freevariode/FreeVarioGauge/src/FreeVarioGauge/data/FreeVario_194x156.bmp

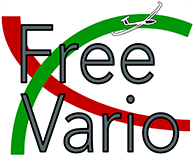
src/FreeVarioGauge/data/FreeVario_194x156.bmp
