freevariode/FreeVarioGauge/src/FreeVarioGauge/FreeVarioGauge.ino

//    OpenVarioGauge is a programm to generate the vario display using NMEA Output
//    of OpenVario.
//    Copyright (C) 2019  Dirk Jung Blaubart@gmx.de
//
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
//*************************************************
//****  Screen and SPIFFS Headers and Defines  ****
//*************************************************
#include <Streaming.h>
#include <WiFi.h>
#include <WebServer.h>
#include <ESPmDNS.h>
#include <Update.h>
#include <SPI.h>
#include <TFT_eSPI.h>
#include <Preferences.h>
Preferences prefs;

#include "LogoOV.h"
#include "FS.h"
#include "SPIFFS.h"
#include <ESP32Encoder.h>

ESP32Encoder Vario_Enc;

#define RXD2 16                // PIN 27
#define TXD2 17                // PIN 28
#define VE_PB 27               // PIN 12
#define DEG2RAD 0.0174532925
#define STF_MODE 13            // PIN 16
#define STF_AUTO 33            // PIN 9
#define OuterRadius 160
#define InnerRadius 130
#define xCenter 160
#define yCenter 160
#define BLUE 0x04df

static TFT_eSPI tft = TFT_eSPI();
TFT_eSprite nameOfField = TFT_eSprite(&tft);
TFT_eSprite Name = TFT_eSprite(&tft);
TFT_eSprite smallFont = TFT_eSprite(&tft);
TFT_eSprite needleGreen = TFT_eSprite(&tft);
TFT_eSprite needleBlue = TFT_eSprite(&tft);
TFT_eSprite drawOuterLine = TFT_eSprite(&tft);
TFT_eSprite drawColoredArc = TFT_eSprite(&tft);
TFT_eSprite drawRectangle = TFT_eSprite(&tft);
TFT_eSprite number = TFT_eSprite(&tft);
TFT_eSprite background = TFT_eSprite(&tft);
WebServer server(80);

Print &cout = Serial;
TaskHandle_t SerialScanTask, TaskValueRefresh;

SemaphoreHandle_t xTFTSemaphore;

long NOT_SET = -1;
long pushButtonPressTime = NOT_SET;

const String SOFTWARE_VERSION = "  V2.4.4 - 2025";

const char *host = "FreeVario_Displayboard";
const char *ssid = "FV_Displayboard";
const char *password = "12345678";


String displayMode = "Waiting ...";
String soundMode = "Waiting ...";
String displayIP = "";
String soundIP = "";
String nameSetting = "QNH";
String nameSpeed = "NA";
String nameHight = "NA";
String stf_mode = "Vario";
String valueQnhAsString = "1013";
String valueBugAsString = "0";
String valueMuteAsString = "NA";
String valueWindAsString = "NA";
String valueSTFAsString = "NA";
String valueAttenAsString = "2";
String valueGrsAsString = "0";
String valueTasAsString = "0";
String valueVaaAsString = "+0.0";
String valueVanAsString = "+0.0";
String valueHigAsString = "0";
String valueFLAsString = "0";
String valueHagAsString = "0";
String valueAwsAsString = "0";
String valueCwsAsString = "0";
String valueMacAsString = "0.0";
String voltage = "0.0";
String UTC = "00:00";
String UTCHour = "00";
String UTCMinute = "00";
String valueVoltageAsString = "0.0";

extern uint16_t logoOV[];

float var = 0;
float stf = 0.0;
float valueTasAsFloat = 0;
float valueMacAsFloat = 0.5;
float valueAwsAsFloat = -1000;
float valueCwsAsFloat = -1000;
float valueAwdAsFloat = -1000;
float valueCwdAsFloat = -1000;
float valueHeaAsFloat = 0;
float encoderPosition = (float) - 999;
float menuActiveSince = 0;                  // Will be updated in menu run

double valueQnhAsFloat = 1013;
double valueBugAsFloat = 0;

bool loadMenuFont = true;
bool loadMenuArc = true;
bool updatemode = false;
bool showBootscreen = true;
bool mci = false;
bool pushButtonIsLongpress = false;
bool pushButtonIsShortpress = false;
bool pushButtonPressed = false;
bool encoderLeft = false;
bool encoderRight = false;
bool encoderWasMoved = false;
bool menuWasTriggered = false;
bool subMenuTriggered = false;
bool subMenuLevelTwoTriggered = false;
bool requestMenuPaint = false;
bool WasSend = false;
bool AutoWasSend = false;
bool SourceIsXCSoar = false;
bool SourceIsLarus = false;

int MENU_SPEED_TYP = 1;
int MENU_HIGHT_TYP = 2;
int MENU_VALUE_TYP = 3;
int MENU_VALUE_QNH = 1;
int MENU_VALUE_BUG = 2;
int MENU_VALUE_MUTE = 3;
int k = 0;
int stf_mode_state;
int startAngle, segmentDraw, segmentCount;
int Wificount = 0;
int valueMuteAsInt;
int valueAttenAsInt;
int valueWindAsInt;
int valueSTFAsInt;
int changeMode;
int oldChangeMode;
int offset = 0;
int selectedMenu = MENU_SPEED_TYP;
int requestDrawMenu = 1;
int requestDrawMenuLevel = 0;
int TimeDifference = 0;

unsigned long lastTimeBoot = 0;
unsigned long lastTimeReady = 0;
unsigned long mcSend  = 0;
unsigned long stayAlive = 0;

// ************************************
// ****  Initialize SPIFFS memory  ****
// ************************************
void SPIFFSstart() {
  if (!SPIFFS.begin()) {
    Serial.println("SPIFFS initialisation failed!");
    while (1) yield(); // Stay here twiddling thumbs waiting
  }
  Serial.println("\r\nInitialisation done.");
}
