freevariode/FreeVarioGauge/src/FreeVarioGauge/LogoOV.h

#include <pgmspace.h>

uint16_t logoOV[] PROGMEM = {
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

};
