freevariode/FreeVarioGauge/src/VarioSound_V2.x/SerialScan.ino

//****************************
//****  read serial port  ****
//****************************
void SerialScan () {
  unsigned long lastTimeSerial2 = 0;
  if (updatemode == false) {
    WiFi.mode(WIFI_OFF);
    char Data;
    String DataString;
    if (Serial2.available()) {
      Data = Serial2.read();
      if (Data == '$') {
        while (Data != 10) {
          if (Data >= 32 && Data <= 126) {
            DataString += Data;
          }
          Data = Serial2.read();
        }
        startSound = true;
        //Serial.println(DataString);
      }
      else {
        if ((!SourceIsXCSoar && !SourceIsLarus) && (baudDetect == 0) && (millis() - ChangeBaud <= 5000)) {
          Serial2.end();
          Serial.println("Looking for XCSoar");
          Serial.println("baud rate is set to 115200");
          Serial2.begin(115200, SERIAL_8N1, RXD2, TXD2);
          delay(500);
          baudDetect = 1;
        }
        else if ((!SourceIsXCSoar && !SourceIsLarus) && (baudDetect == 1) &&  (millis() - ChangeBaud > 5000) && (millis() - ChangeBaud <= 10000)) {
          Serial2.end();
          Serial.println("Looking for Larus");
          Serial.println("baud rate is set to 38400");
          Serial2.begin(38400, SERIAL_8N1, RXD2, TXD2);
          delay(500);
          baudDetect = 0;
        }
        else if ((!SourceIsXCSoar && !SourceIsLarus) && (millis() - ChangeBaud > 10000)) {
          ChangeBaud = millis();
        }
      }

      //****************************
      //****  XCSoar is source  ****
      //****************************
      if ((DataString.startsWith("$PFV,VAR")) || (DataString.startsWith("$PFV,VAN"))) {
        if (!SourceIsXCSoar) {
          SourceIsXCSoar = true;
          SourceIsLarus = false;
        }
      }

      if (DataString.startsWith("$PFV") && SourceIsXCSoar == true) {
        //Serial2.println(DataString);
        int pos = DataString.indexOf(',');
        DataString.remove(0, pos + 1);
        int pos1 = DataString.indexOf(',');                   //finds the place of the first,
        String variable = DataString.substring(0, pos1);      //captures the first record
        int pos2 = DataString.indexOf('*', pos1 + 1 );        //finds the place of *
        String wert = DataString.substring(pos1 + 1, pos2);   //captures the second record

        //**************************************
        //****  Analysis of the climb rate  ****
        //**************************************
        if (variable == "VAR") {
          var = wert.toFloat();
          varAvailable = true;
        }

        //***********************************************
        //****  Analysis of the current XCSoar mode  ****
        //***********************************************
        if (variable == "MOD") {
          mod = wert;
        }

        //*******************************************************
        //****  Analysis of the current Remote control mode  ****
        //*******************************************************
        if (variable == "REM") {
          rem = wert;
        }

        //*****************************************
        //****  Analysis of the true airspeed  ****
        //*****************************************
        if (variable == "TAS") {
          tas = wert.toFloat();
        }

        //************************************
        //****  Analysis of speed to fly  ****
        //************************************
        if (variable == "STF") {
          stfValue = wert.toFloat();
          if (tas > 10) {
            int FF = (valueAttenAsInt * 10) + 1;
            stf = filter(stfValue, FF);
          }
          else {
            stf = tas;
          }
        }

        //*************************
        //****  Analysis Mute  ****
        //*************************
        else if (variable == "MUT") {
          valueMuteAsInt = wert.toInt();
        }

        //********************************
        //****  Analysis Attenuation  ****
        //********************************
        else if (variable == "ATT") {
          valueAttenAsInt = wert.toInt();
        }

        //*******************************
        //****  analyse STF-Mode  ****
        //*******************************
        else if (variable == "SMO") {
          valueSTFAsInt = wert.toInt();
        }

        sf = (tas - stf) / 10;
      }

      //***************************
      //****  Larus is source  ****
      //***************************
      if (DataString.startsWith("$PLAR")) {
        if (!SourceIsLarus == true) {
          SourceIsLarus = true;
          SourceIsXCSoar = false;
        }
        if (DataString.startsWith("$PLARV")) {
          int pos0 = DataString.indexOf('*');
          String dataToCheck = DataString.substring(0, pos0);
          DataString.remove(0, pos0 + 1);
          String CheckSum = DataString;
          CheckSum.toLowerCase();
          CheckSum.trim();
          int checksum = calculateChecksum(dataToCheck);
          String checksumString = String(checksum, HEX);
          if (CheckSum == checksumString) {
            lastTimeSerial2 = millis();
            //Serial2.println(dataString);
            dataToCheck.remove(0, 7);
            int pos1 = dataToCheck.indexOf(',');                   //findet den Ort des ersten ,
            String VAR = dataToCheck.substring(0, pos1);           //erfasst das aktuelle Steigen
            var = VAR.toFloat();                                   //wandelt das aktuelle Steigen in float
            varAvailable = true;

            int pos2 = dataToCheck.indexOf(',', pos1 + 1);         //findet den Ort des zweiten ,
            int pos3 = dataToCheck.indexOf(',', pos2 + 1);         //findet den Ort des dritten ,
            int pos4 = dataToCheck.indexOf(',', pos3 + 1);         //findet den Ort des vierten ,

            String TAS = dataToCheck.substring(pos3 + 1, pos4);    //erfasst die TAS
            valueTasAsFloat = TAS.toFloat();                       //wandelt die TAS in float
            char buf2[20];
            // dtostrf(floatvar, stringlength, digits_after_decimal, charbuf);
            valueTasAsString = dtostrf(valueTasAsFloat, 3, 0, buf2);
          }
        }
      }
      DataString = "";
      vTaskDelay(20);
    }
  }
}
